RobJansen62/Adjustable-constant-current-source-and-constant-current-sink/hardware/Ajustable_Current_Source_Sink.kicad_sch

## KiCad design hardware/Ajustable_Current_Source_Sink.kicad_sch (2025-08-08)

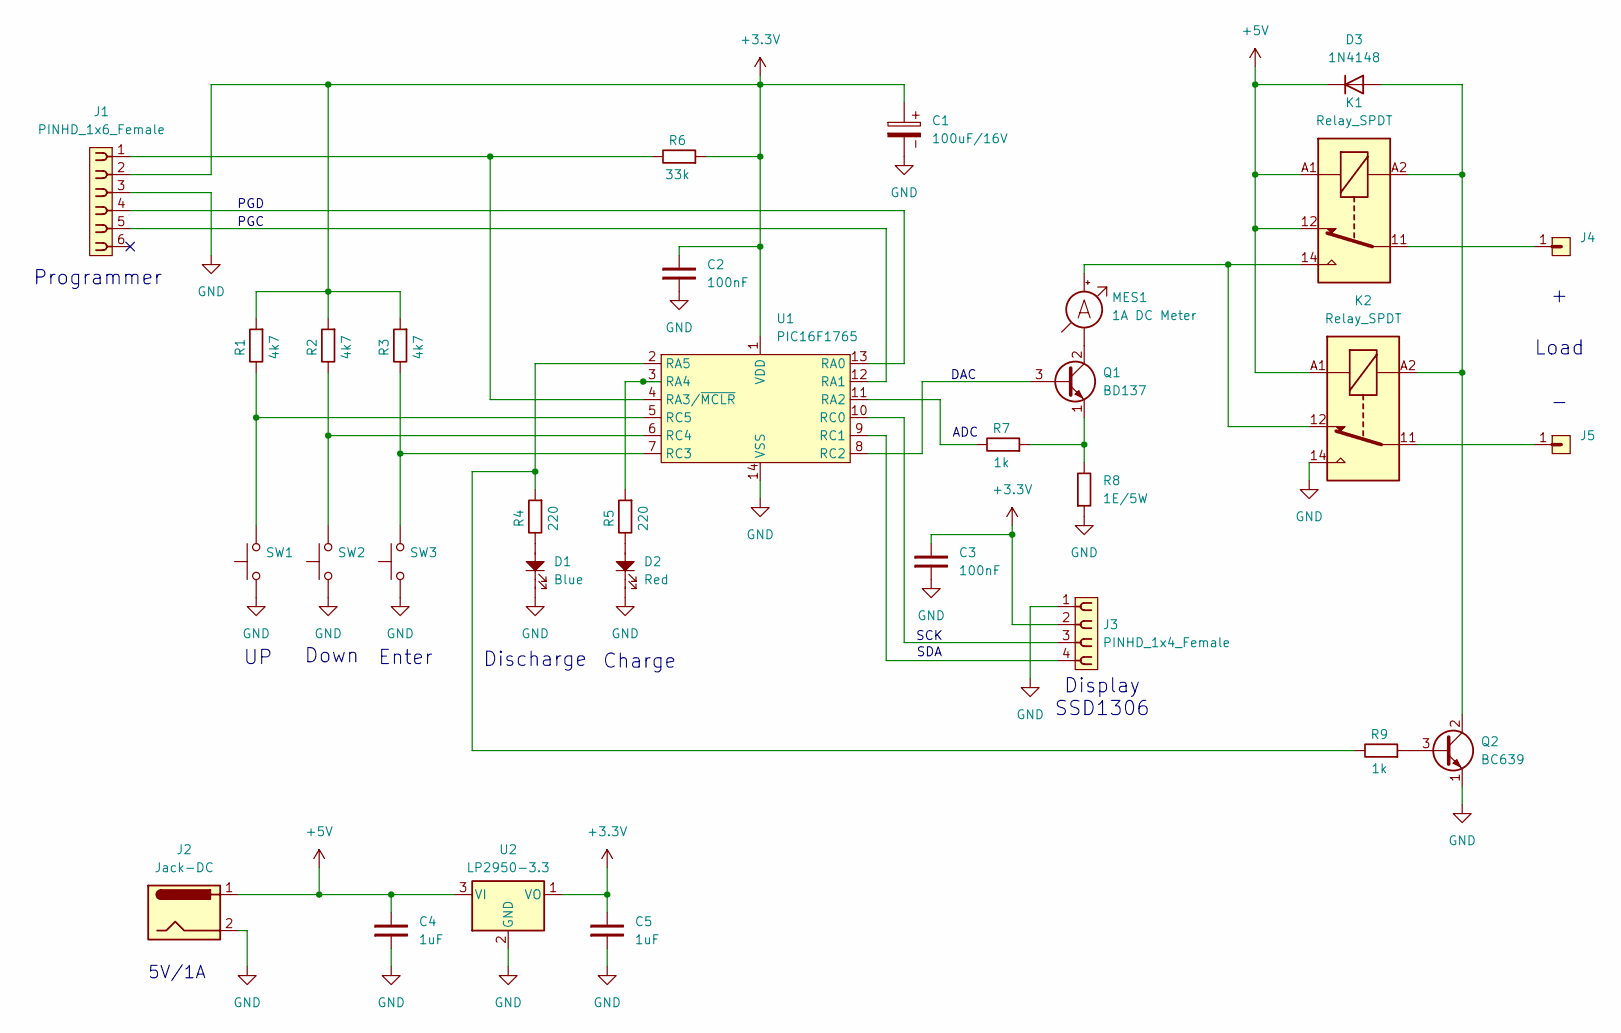
[picture p7: schematic Ajustable_Current_Source_Sink.kicad_sch]

Parts:
C1: 100uF/16V; CP_Radial_D5.0mm_P2.50mm
C2, C3: 100nF; C_Disc_D3.0mm_W2.0mm_P2.50mm
C4, C5: 1uF; C_Disc_D3.0mm_W2.0mm_P2.50mm
D1: Blue; LED_D5.0mm
D2: Red; LED_D5.0mm
D3: 1N4148; D_DO-35_SOD27_P7.62mm_Horizontal
J1: PINHD_1x6_Female; PinSocket_1x06_P2.54mm_Vertical
J2: Jack-DC
J3: PINHD_1x4_Female; PinSocket_1x04_P2.54mm_Vertical
J4, J5: PINHD_1x1_Male; PinHeader_1x01_P2.54mm_Vertical
K1, K2: Relay_SPDT
MES1: 1A DC Meter
Q1: BD137; TO-126-3_Vertical
Q2: BC639; TO-92_Inline
R1, R2, R3: 4k7; R_Axial_DIN0207_L6.3mm_D2.5mm_P10.16mm_Horizontal
R4, R5: 220; R_Axial_DIN0207_L6.3mm_D2.5mm_P10.16mm_Horizontal
R6: 33k; R_Axial_DIN0207_L6.3mm_D2.5mm_P10.16mm_Horizontal
R7, R9: 1k; R_Axial_DIN0207_L6.3mm_D2.5mm_P10.16mm_Horizontal
R8: 1E/5W; R_Axial_DIN0207_L6.3mm_D2.5mm_P10.16mm_Horizontal
SW1, SW2, SW3: SW_Push
U1: PIC16F1765; CERDIP-14_W7.62mm_SideBrazed_LongPads_Socket
U2: LP2950-3.3; TO-92_Inline

Connections:
+3.3V: C1.1, C2.2, C3.2, C5.2, J1.2, J3.2, R1.1, R2.1, R3.1, R6.1, U1.1 (VDD), U2.1 (VO)
+5V: C4.2, D3.1 (K), J2.1, K1.12, K1.A1, K2.A1, U2.3 (VI)
GND: C1.2, C2.1, C3.1, C4.1, C5.1, D1.1, D2.1, J1.3, J2.2, J3.1, K2.14, Q2.1 (E), R8.1, SW1.1, SW2.1, SW3.1, U1.14 (VSS), U2.2 (GND)
unnamed: D1.2, R4.2
unnamed: D2.2, R5.2
unnamed: D3.2 (A), K1.A2, K2.A2, Q2.2 (C)
unnamed: J1.1, R6.2, U1.4 (RA3/~MCLR)
unnamed: J1.4, U1.13 (RA0)
unnamed: J1.5, U1.12 (RA1)
unnamed: J3.3, U1.10 (RC0)
unnamed: J3.4, U1.9 (RC1)
unnamed: J4.1, K1.11
unnamed: J5.1, K2.11
unnamed: K1.14, K2.12, MES1.2 (+)
unnamed: MES1.1 (-), Q1.2 (C)
unnamed: Q1.1 (E), R7.1, R8.2
unnamed: Q1.3 (B), U1.8 (RC2)
unnamed: Q2.3 (B), R9.1
unnamed: R1.2, SW1.2, U1.5 (RC5)
unnamed: R2.2, SW2.2, U1.6 (RC4)
unnamed: R3.2, SW3.2, U1.7 (RC3)
unnamed: R4.1, R9.2, U1.2 (RA5)
unnamed: R5.1, U1.3 (RA4)
unnamed: R7.2, U1.11 (RA2)

Notes on the sheet:
5V/1A
DAC
PGD
Load
SDA
Programmer
PGC
Display SSD1306
Down
SCK
Charge
ADC
Discharge
Enter
